sarathr7051-lab/jiffytrails-navigator/firmware/navigator/watchdog.cpp

/*
  watchdog.cpp — freshness and link state.

  The rule that makes this work: count packet ARRIVALS, not value changes.
  NAV_DATA.md measured 64 seconds in slow traffic during which not one field
  changed, while Maps kept posting at ~1 Hz — the distance was simply
  quantised to 100 m steps and the road name was the same. A change-based
  watchdog has no threshold that survives that. An arrival-based one is happy
  at 10 s.
*/

#include "watchdog.h"
#include "ble.h"

void watchdogNotePacket(NavState& s) {
  s.lastPacketMs = millis();
  s.packetCount++;
  s.stale = false;
}

void watchdogTick(NavState& s) {
  const bool wasUp = s.linkUp;
  s.linkUp = bleConnected();

  // A fresh connection restarts the clock. Without this, a device that sat
  // disconnected for a minute would come back already "stale" and flash the
  // warning before the first packet had any chance to arrive.
  if (s.linkUp && !wasUp) {
    s.lastPacketMs = millis();
    s.stale = false;
    /*
      ★ AND WIPE THE NAV CONTENT. Restarting the clock without clearing what it
      vouches for was the other half of the same defect: the flags, maneuver,
      distance and road name all survived a disconnect, so a reconnect hours
      later re-validated yesterday's turn and rendered it as live.

      A reconnect now lands on IDLE and stays there until real NAV arrives.
    */
    s.flags        = 0;
    s.maneuver     = MV_UNKNOWN;
    s.dist_m       = 0;
    s.next_maneuver = MV_UNKNOWN;
    s.next_dist_m  = 0;
    s.instruction[0] = 0;
    s.lastNavMs    = millis();

    /*
      ★ AND THE ALERTS, WHICH WERE THE HALF LEFT BEHIND.

      callState is persistent state with no timestamp - by design, because a
      ring has to stay on screen until it stops. The phone clears it by sending
      PKT_CALL with CALL_IDLE, and it only sends PKT_CALL on a state CHANGE.

      So: pull the phone out of a jacket pocket while it is ringing, the link
      drops mid-ring, and the CALL_IDLE that would have cleared it is sent to
      nobody. On reconnect bandFor sees callState != CALL_IDLE and floods the
      whole screen inverted with "CALL / <name>" - a call that is not
      happening, over the navigation, until the next real call or a power
      cycle. DISCONNECTED outranking the band hides this only while the link is
      down; the reconnect is exactly when it surfaces.

      The notification fields are dwell-bounded and so cannot hang the same
      way, but they are stale by the same argument and go with it: what the
      restarted freshness clock now vouches for is nothing at all.
    */
    s.callState    = CALL_IDLE;
    s.callName[0]  = 0;
    s.notifyText[0] = 0;
    s.notifySrc[0]  = 0;
  }

  // While the link is down, DISCONNECTED outranks STALE anyway (see
  // screenFor). Hold the timer so the two states can never both be showing.
  if (!s.linkUp) {
    s.lastPacketMs = millis();
    s.stale = false;
    return;
  }

  /*
    ★ TWO CLOCKS, EITHER ONE CAN GO STALE.

    lastPacketMs says the link is alive. lastNavMs says the maneuver is. The
    nav screens must gate on BOTH, because the phone sends STATUS every 30 s
    regardless of whether Maps is still producing anything - so the link clock
    alone would report "fresh" over a maneuver that died half an hour ago.
  */
  const uint32_t now = millis();
  s.stale = (now - s.lastPacketMs) > STALE_MS
         || (s.navActive() && (now - s.lastNavMs) > STALE_MS);

  // Arrival latch. Maps drops its notification about 4.7 s after you arrive,
  // which clears nav_active — so without latching, the arrival screen would
  // flash past and settle on IDLE, and the one moment the device should
  // acknowledge would be the one it skipped.
  if (s.arrived()) {
    if (!s.showArrival && s.arrivedAtMs == 0) {
      s.arrivedAtMs = millis();
      s.showArrival = true;
    }
    if (s.showArrival && (millis() - s.arrivedAtMs) > ARRIVAL_DWELL_MS) {
      s.showArrival = false;
    }
  } else {
    // A new route clears the latch so the next arrival can fire.
    s.showArrival = false;
    s.arrivedAtMs = 0;
  }
}
